Prorifi3D-Official/Prorifi3D-Upgrades/tmp/pdfs/assets-contact-sheet.jpg

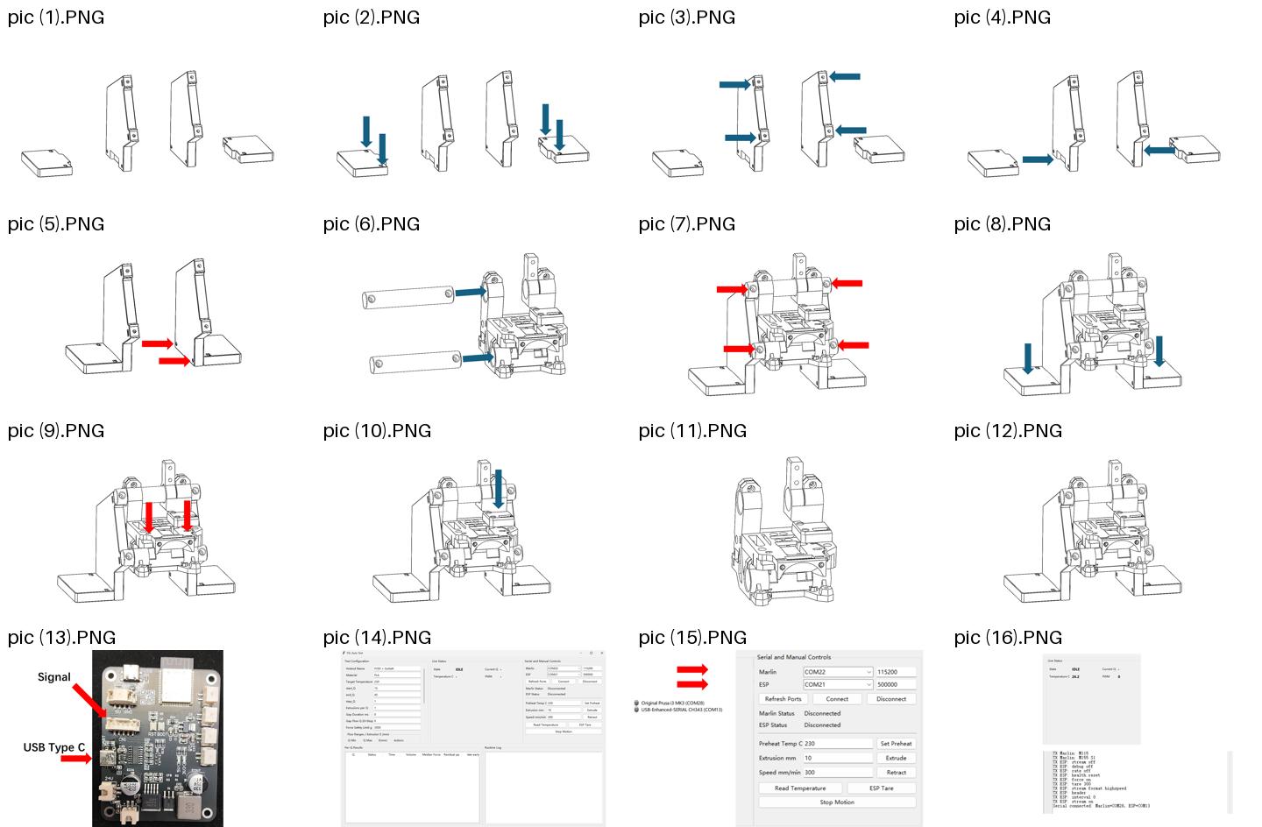
tmp/pdfs/assets-contact-sheet.jpg
