Prorifi3D-Official/Prorifi3D-Upgrades/tmp/pdfs/extracted/page-10-image-01.png

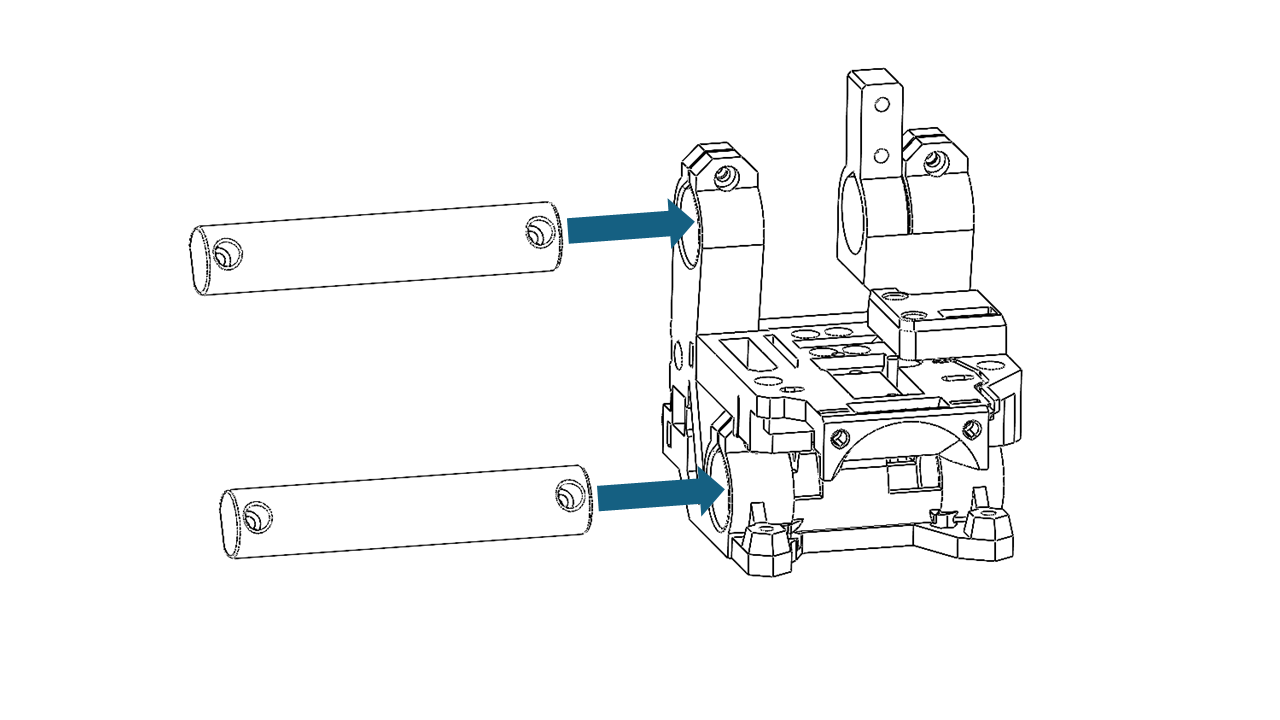
tmp/pdfs/extracted/page-10-image-01.png
