Prorifi3D-Official/Prorifi3D-Upgrades/tmp/pdfs/extracted/page-11-image-02.png

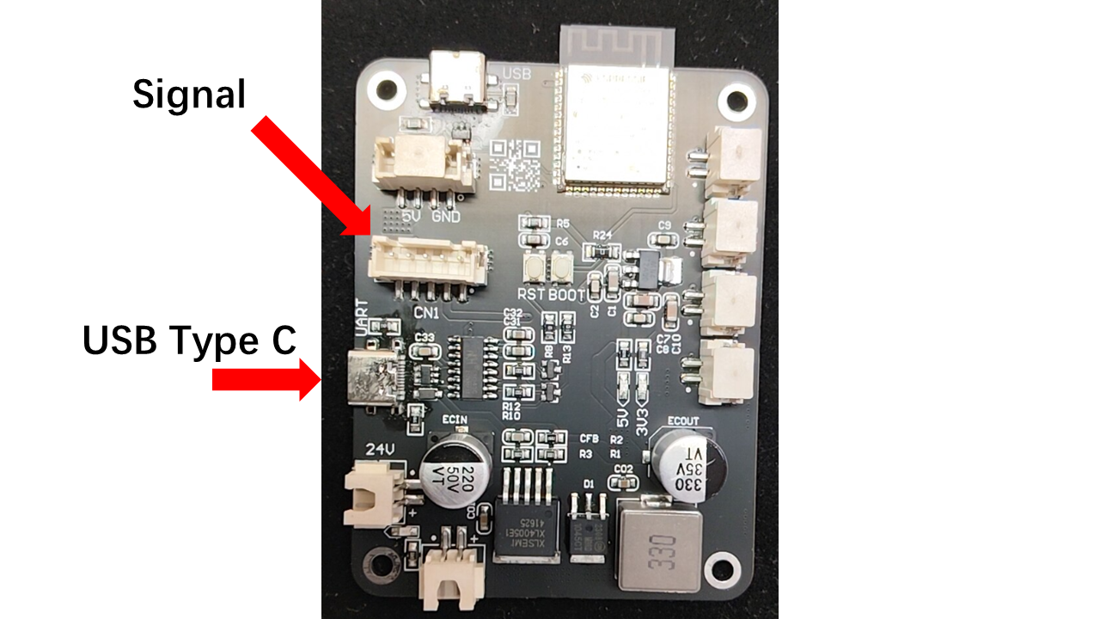
tmp/pdfs/extracted/page-11-image-02.png
