Prorifi3D-Official/Prorifi3D-Upgrades/tmp/pdfs/extracted/page-15-image-02.png

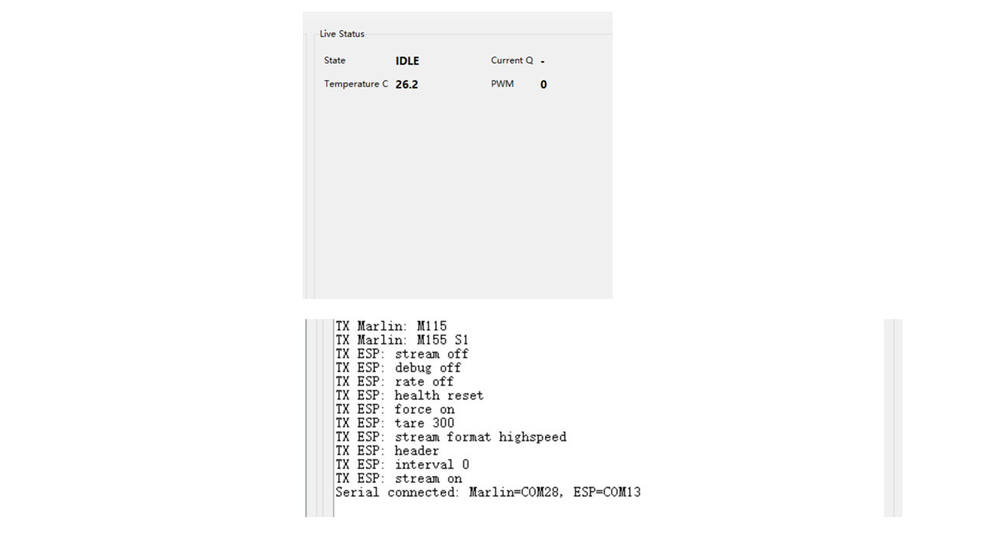
tmp/pdfs/extracted/page-15-image-02.png
