Prorifi3D-Official/Prorifi3D-Upgrades/tmp/pdfs/pdf-pages-contact-sheet.jpg

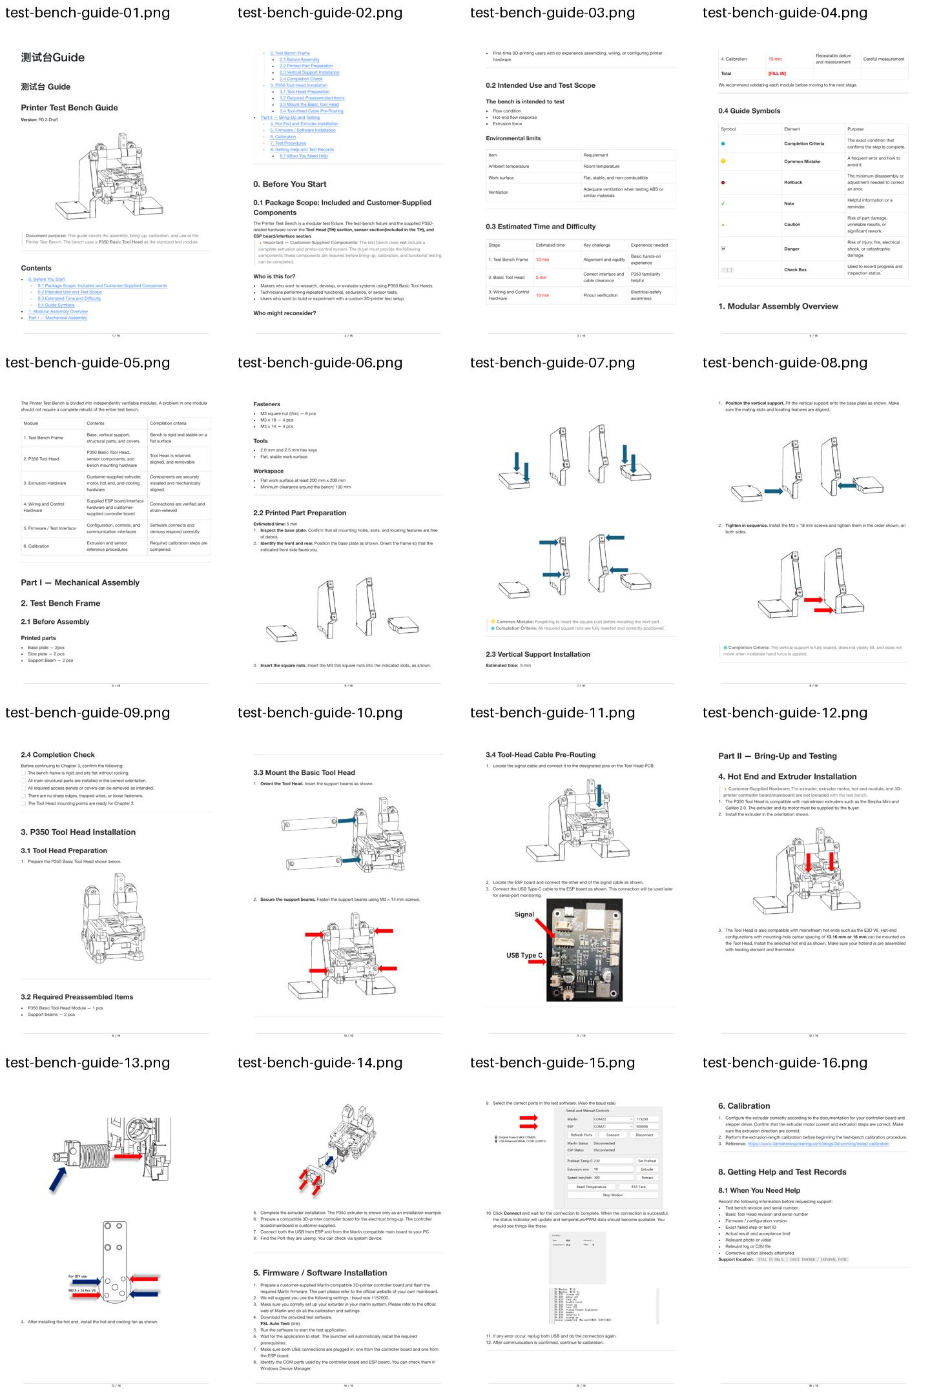
tmp/pdfs/pdf-pages-contact-sheet.jpg
