Prorifi3D-Official/Prorifi3D-Upgrades/tmp/site/src/assets/Dual_Belt_Plus/DB+6.JPG

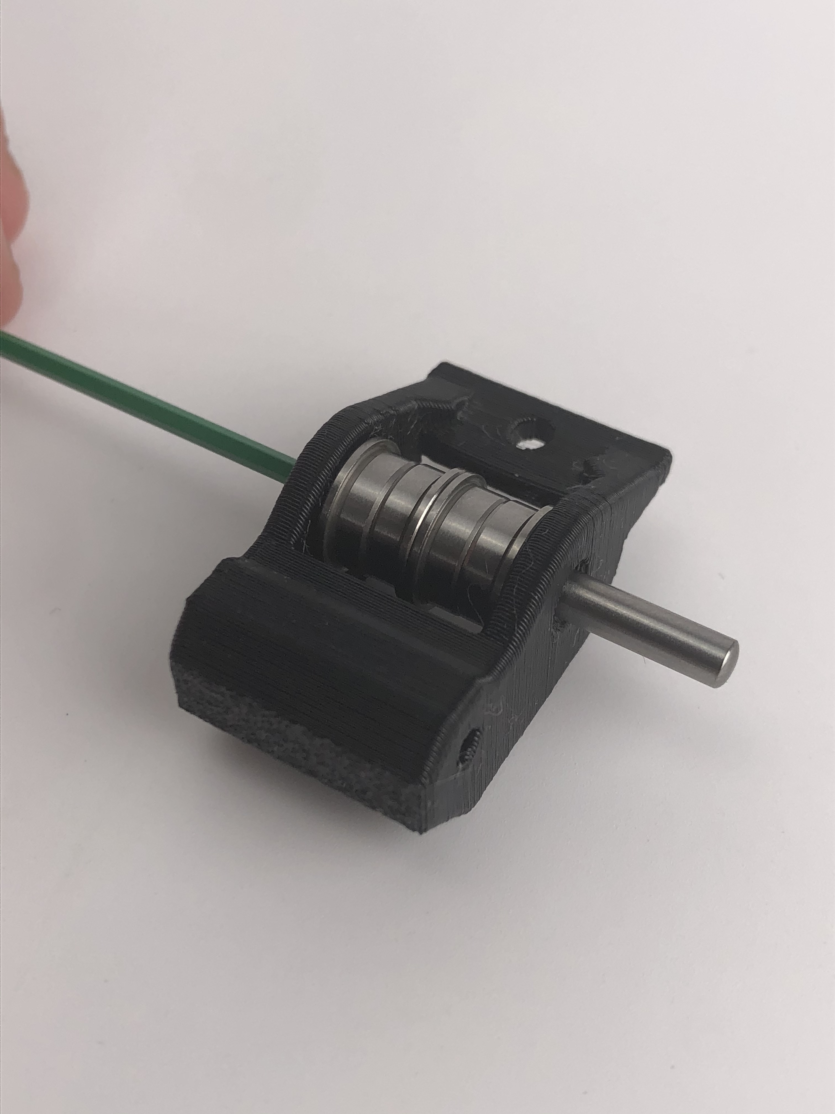
tmp/site/src/assets/Dual_Belt_Plus/DB+6.JPG
