Prorifi3D-Official/Prorifi3D-Upgrades/tmp/site/src/assets/Dual_Belt_Plus/DB+7.JPG

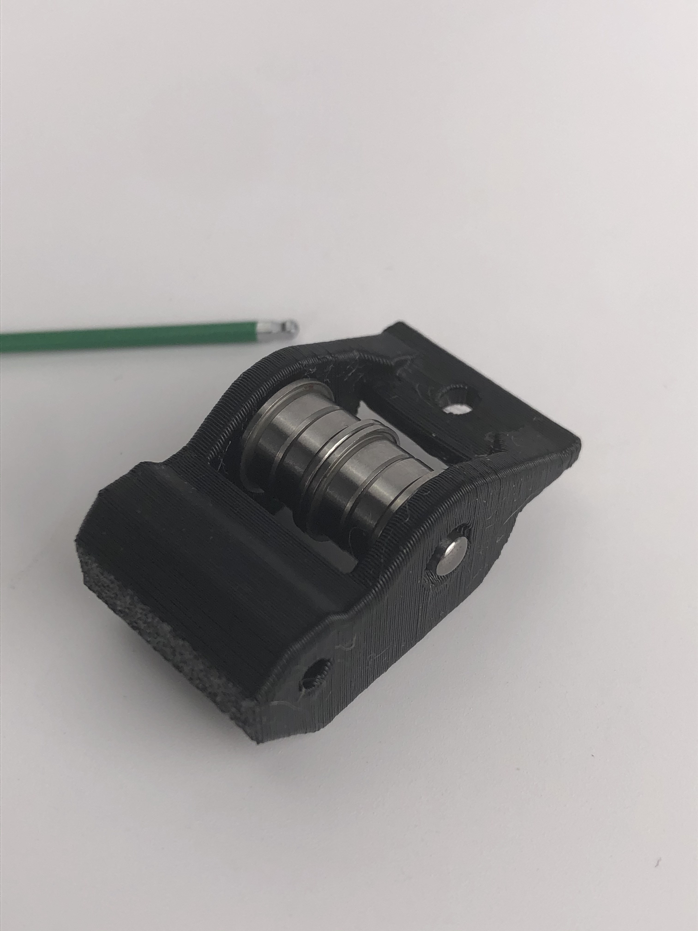
tmp/site/src/assets/Dual_Belt_Plus/DB+7.JPG
