Prorifi3D-Official/Prorifi3D-Upgrades/tmp/site/src/assets/Stage_2/DB_1.png

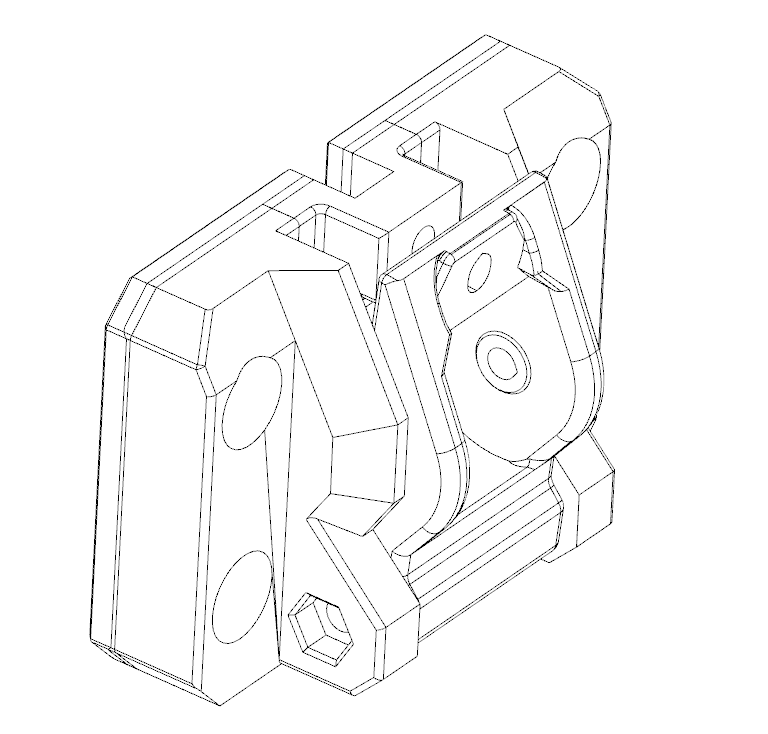
tmp/site/src/assets/Stage_2/DB_1.png
