Prorifi3D-Official/Prorifi3D-Upgrades/tmp/site/src/assets/Stage_2/PSU_2.png

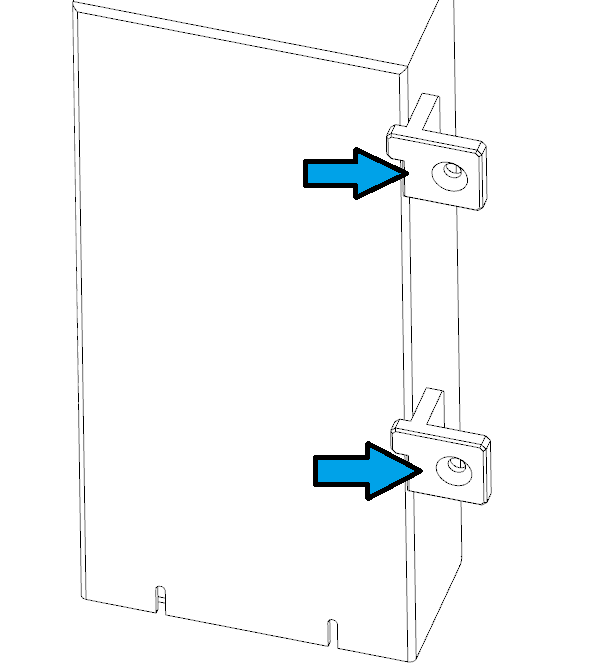
tmp/site/src/assets/Stage_2/PSU_2.png
