Prorifi3D-Official/Prorifi3D-Upgrades/Original i3 series Upgrade Kits/Stage 2 Upgrade/Frame/STL/BLACK/3mf/Spool_holder.3mf

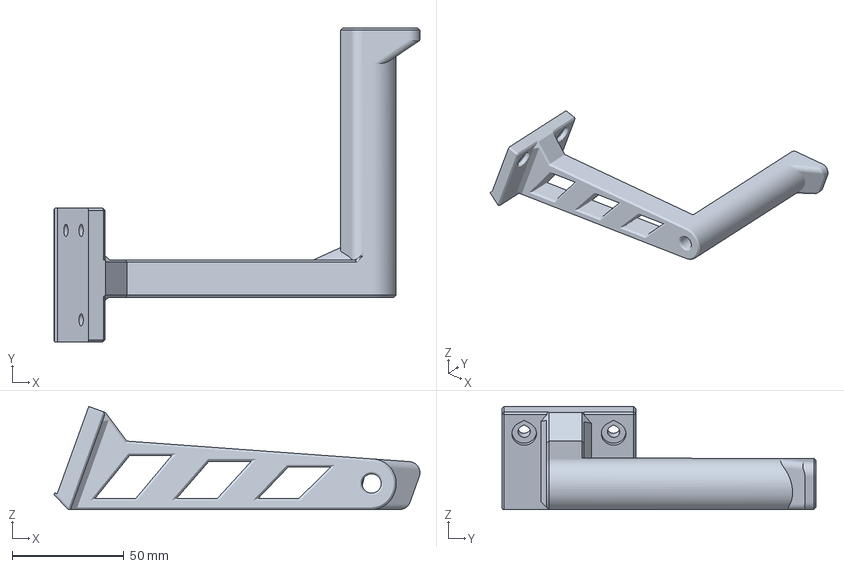
[picture p133: CAD file, 2022-03-23]
Original i3 series Upgrade Kits/Stage 2 Upgrade/Frame/STL/BLACK/3mf/Spool_holder.3mf
163.7 x 140.6 x 46.1 mm
