Prorifi3D-Official/Prorifi3D-Upgrades/Original i3 series Upgrade Kits/Stage 2 Upgrade/Frame/STL/Jigs/Jigs.3mf

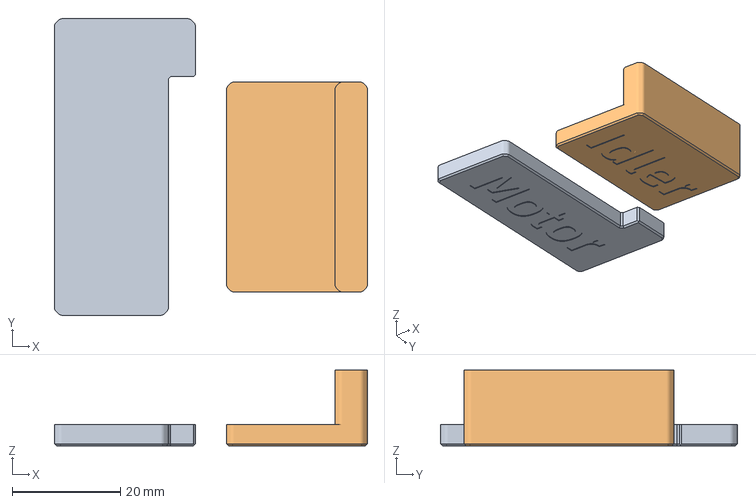
[picture p134: CAD file, 2022-03-23]
Original i3 series Upgrade Kits/Stage 2 Upgrade/Frame/STL/Jigs/Jigs.3mf
57.7 x 54.7 x 14.0 mm
Jig-Motor.stl
Jig-Idler.stl
