Prorifi3D-Official/Prorifi3D-Upgrades/Original i3 series Upgrade Kits/Stage 2 Upgrade/Frame/STL/MIX COLOR/LCD-Cover.stl

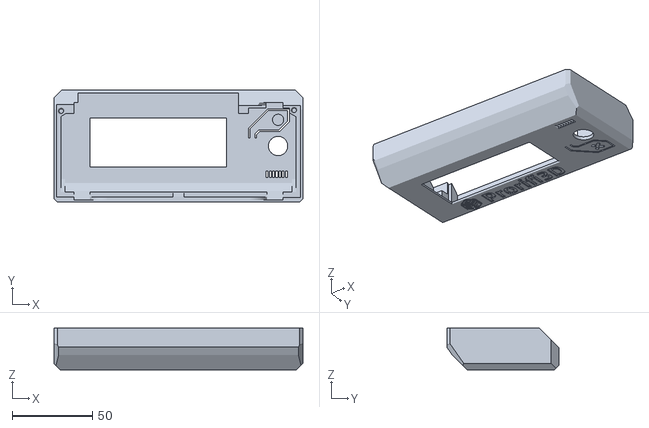
[picture p135: CAD file, 2022-03-23]
Original i3 series Upgrade Kits/Stage 2 Upgrade/Frame/STL/MIX COLOR/LCD-Cover.stl
155.0 x 70.0 x 26.0
