Prorifi3D-Official/Prorifi3D-Upgrades/Original i3 series Upgrade Kits/Stage 2 Upgrade/Frame/STL/WATER BLUE/(4)-Endcover.stl

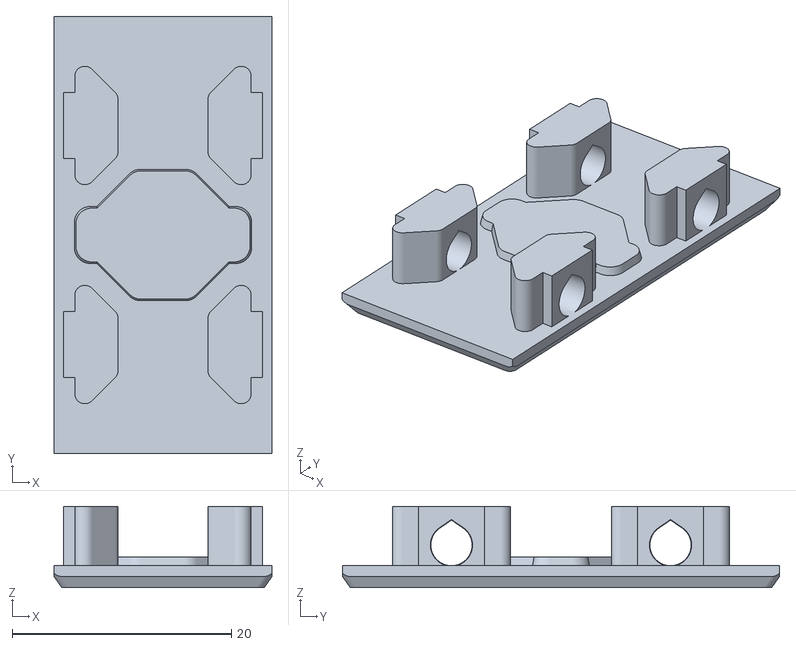
[picture p136: CAD file, 2022-03-23]
Original i3 series Upgrade Kits/Stage 2 Upgrade/Frame/STL/WATER BLUE/(4)-Endcover.stl
19.9 x 39.9 x 7.40
