Prorifi3D-Official/Prorifi3D-Upgrades/Original MINI series Upgrade Kits/MINI Upgrade/Dual Belt/STL/MINI_Y_belt_holder_B.STL

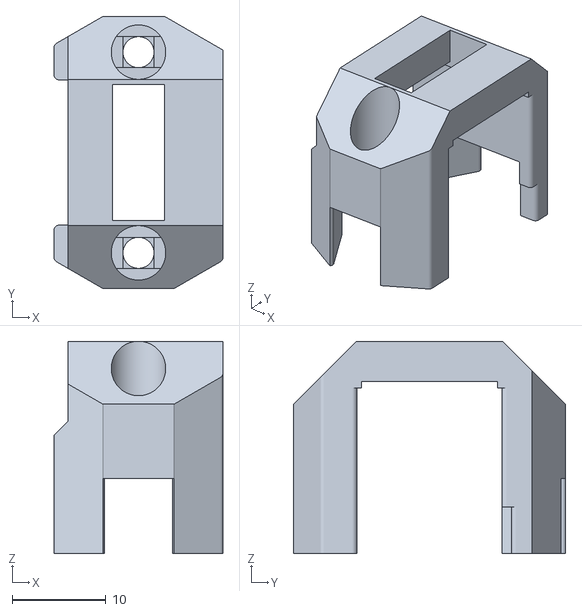
[picture p137: CAD file, 2022-11-03]
Original MINI series Upgrade Kits/MINI Upgrade/Dual Belt/STL/MINI_Y_belt_holder_B.STL
18.0 x 29.0 x 22.7
