Prorifi3D-Official/Prorifi3D-Upgrades/Original i3 series Upgrade Kits/Stage 1 Upgrade/Dual Belt/STEP/Y-Belt-Idler-B.step

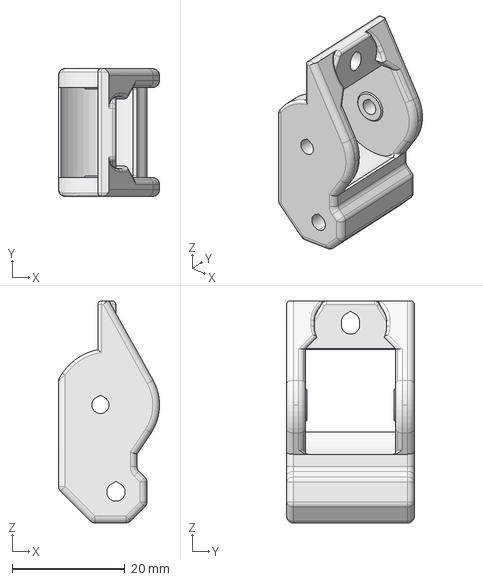
[picture p138: CAD file, 2022-03-23]
Original i3 series Upgrade Kits/Stage 1 Upgrade/Dual Belt/STEP/Y-Belt-Idler-B.step
18.0 x 22.7 x 39.4 mm
