Prorifi3D-Official/Prorifi3D-Upgrades/Original i3 series Upgrade Kits/Stage 2 Upgrade/Frame/STL/BLACK/Electronics-Cover-Holder-B.stl

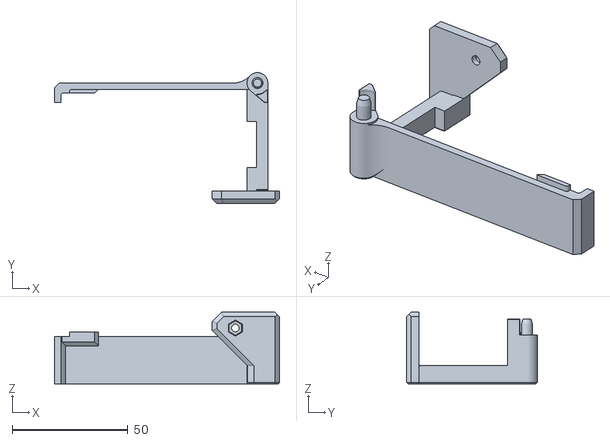
[picture p139: CAD file, 2022-03-23]
Original i3 series Upgrade Kits/Stage 2 Upgrade/Frame/STL/BLACK/Electronics-Cover-Holder-B.stl
97.0 x 56.4 x 31.0
