Prorifi3D-Official/Prorifi3D-Upgrades/Original i3 series Upgrade Kits/Stage 2 Upgrade/Frame/STL/Jigs/Jig-Idler.stl

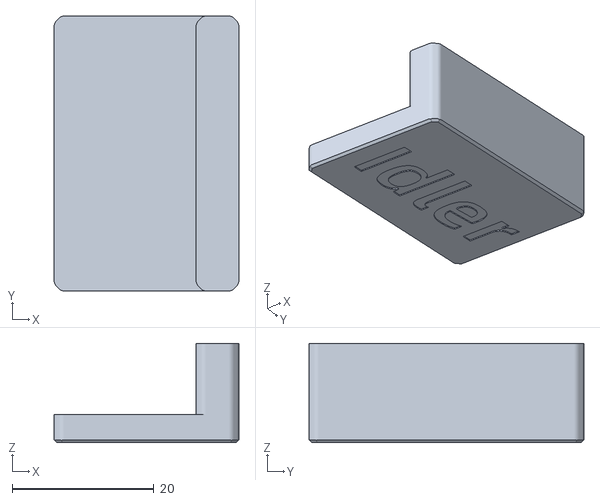
[picture p140: CAD file, 2022-03-23]
Original i3 series Upgrade Kits/Stage 2 Upgrade/Frame/STL/Jigs/Jig-Idler.stl
26.0 x 38.7 x 14.0
