Prorifi3D-Official/Prorifi3D-Upgrades/Original i3 series Upgrade Kits/Stage 2 Upgrade/Frame/STL/WATER BLUE/LCD-Support-A.stl

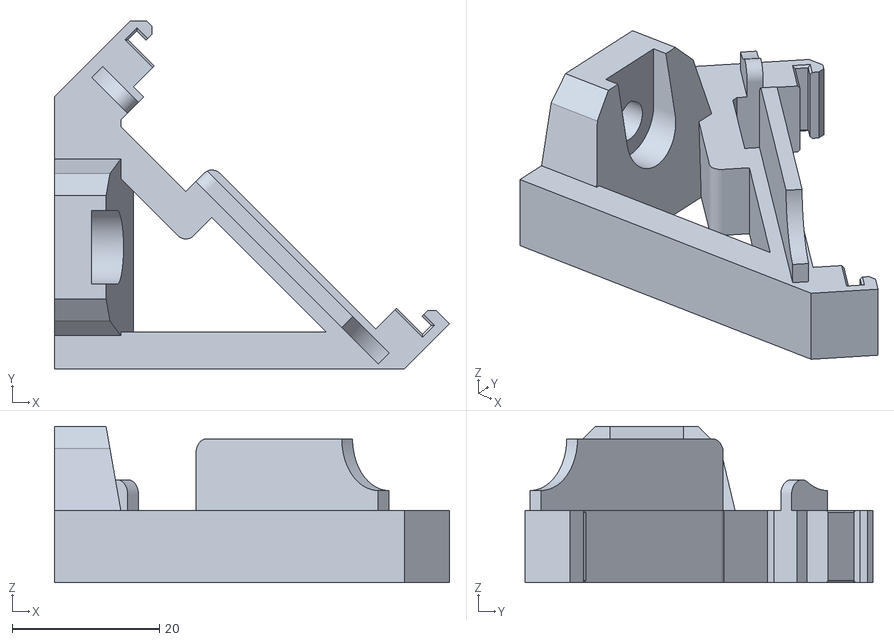
[picture p141: CAD file, 2022-03-23]
Original i3 series Upgrade Kits/Stage 2 Upgrade/Frame/STL/WATER BLUE/LCD-Support-A.stl
53.6 x 47.2 x 21.2
