Prorifi3D-Official/Prorifi3D-Upgrades/Original MINI series Upgrade Kits/MINI Upgrade/Dual Belt/STL/MINI_Y_belt_holder_A.STL

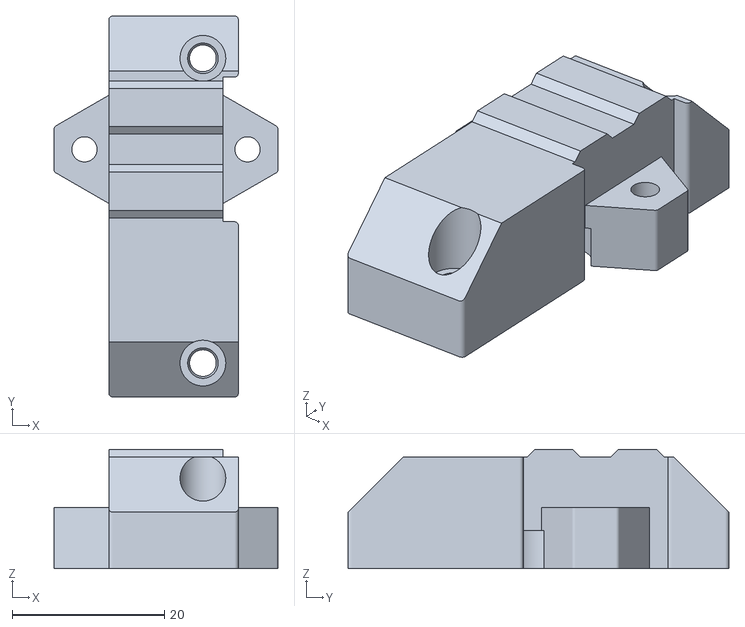
[picture p142: CAD file, 2022-11-03]
Original MINI series Upgrade Kits/MINI Upgrade/Dual Belt/STL/MINI_Y_belt_holder_A.STL
29.4 x 50.0 x 15.6
