Prorifi3D-Official/Prorifi3D-Upgrades/Original i3 series Upgrade Kits/Stage 2 Upgrade/Frame/STL/BLACK/Electronics-Cover-Holder-A.stl

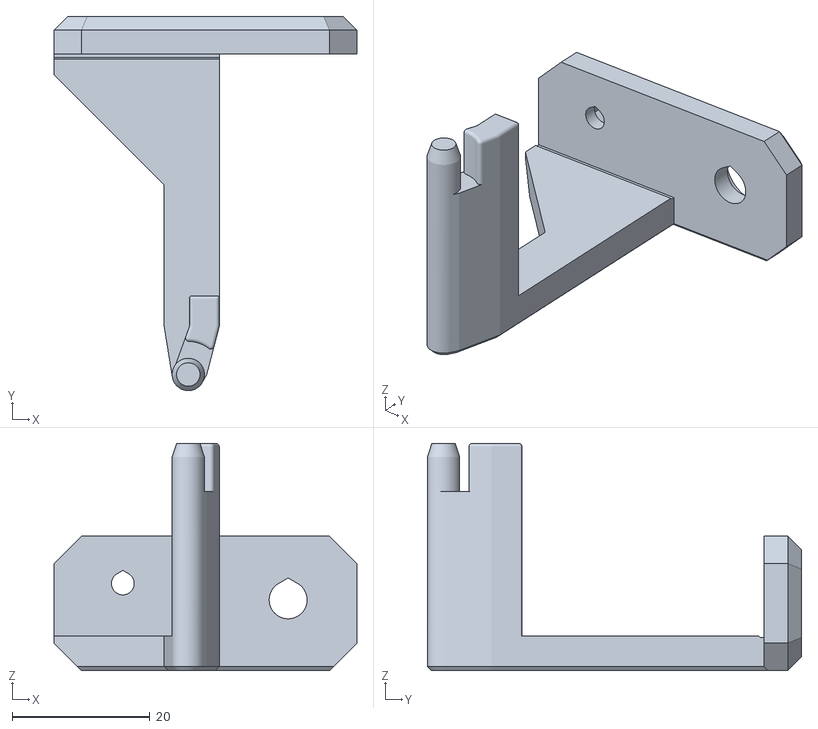
[picture p143: CAD file, 2022-03-23]
Original i3 series Upgrade Kits/Stage 2 Upgrade/Frame/STL/BLACK/Electronics-Cover-Holder-A.stl
44.0 x 54.4 x 33.0
