Prorifi3D-Official/Prorifi3D-Upgrades/Original MINI series Upgrade Kits/MINI Upgrade/Dual Belt/STL/MINI+-Y-idler.STL

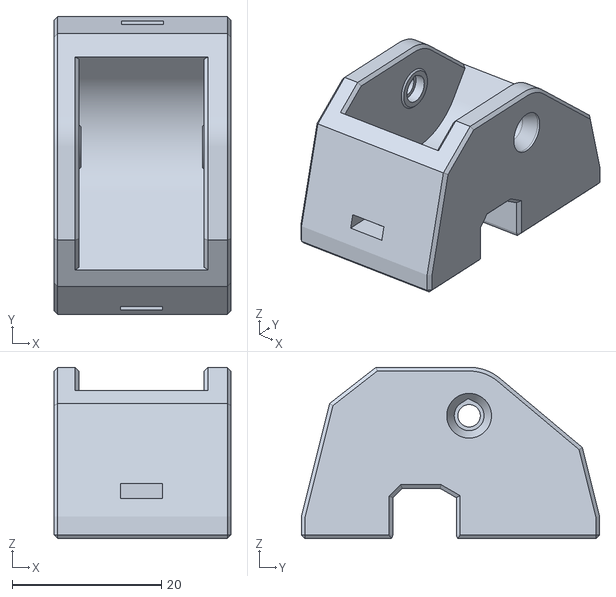
[picture p144: CAD file, 2022-11-01]
Original MINI series Upgrade Kits/MINI Upgrade/Dual Belt/STL/MINI+-Y-idler.STL
23.8 x 40.0 x 23.0
