Prorifi3D-Official/Prorifi3D-Upgrades/Original i3 series Upgrade Kits/Stage 1 Upgrade/Dual Belt/STEP/Y-Belt-Clip.STEP

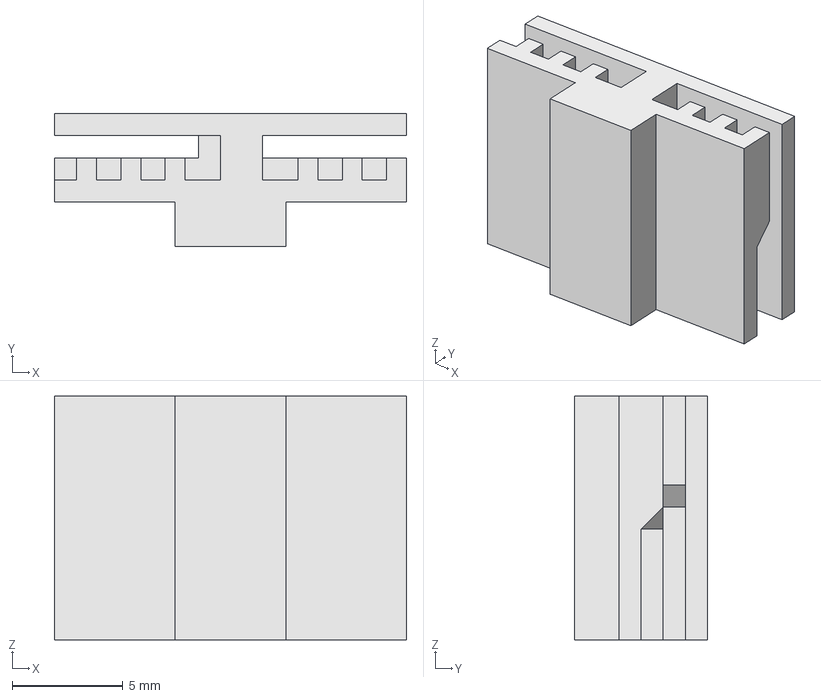
[picture p145: CAD file, 2022-03-23]
Original i3 series Upgrade Kits/Stage 1 Upgrade/Dual Belt/STEP/Y-Belt-Clip.STEP
15.9 x 6.00 x 11.0 mm
