Prorifi3D-Official/Prorifi3D-Upgrades/Original i3 series Upgrade Kits/Stage 2 Upgrade/Frame/STL/BLACK/(2)-Bottomcover.stl

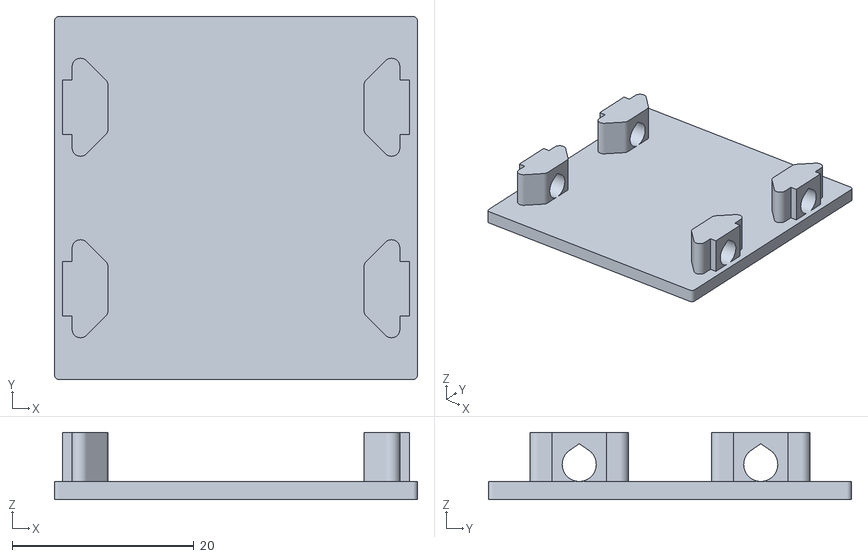
[picture p146: CAD file, 2022-03-23]
Original i3 series Upgrade Kits/Stage 2 Upgrade/Frame/STL/BLACK/(2)-Bottomcover.stl
40.0 x 40.0 x 7.40
