Prorifi3D-Official/Prorifi3D-Upgrades/Original i3 series Upgrade Kits/Stage 2 Upgrade/Frame/STL/WATER BLUE/Y-Belt-Idler-A.stl

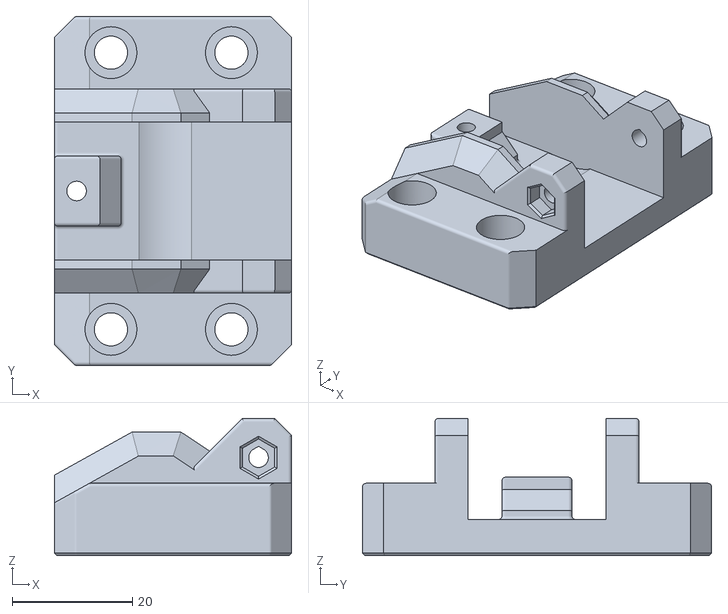
[picture p147: CAD file, 2022-03-23]
Original i3 series Upgrade Kits/Stage 2 Upgrade/Frame/STL/WATER BLUE/Y-Belt-Idler-A.stl
39.4 x 57.9 x 22.8
