Prorifi3D-Official/Prorifi3D-Upgrades/Original i3 series Upgrade Kits/Stage 2 Upgrade/Frame/STL/BLACK/(2)-PSU-Holder.stl

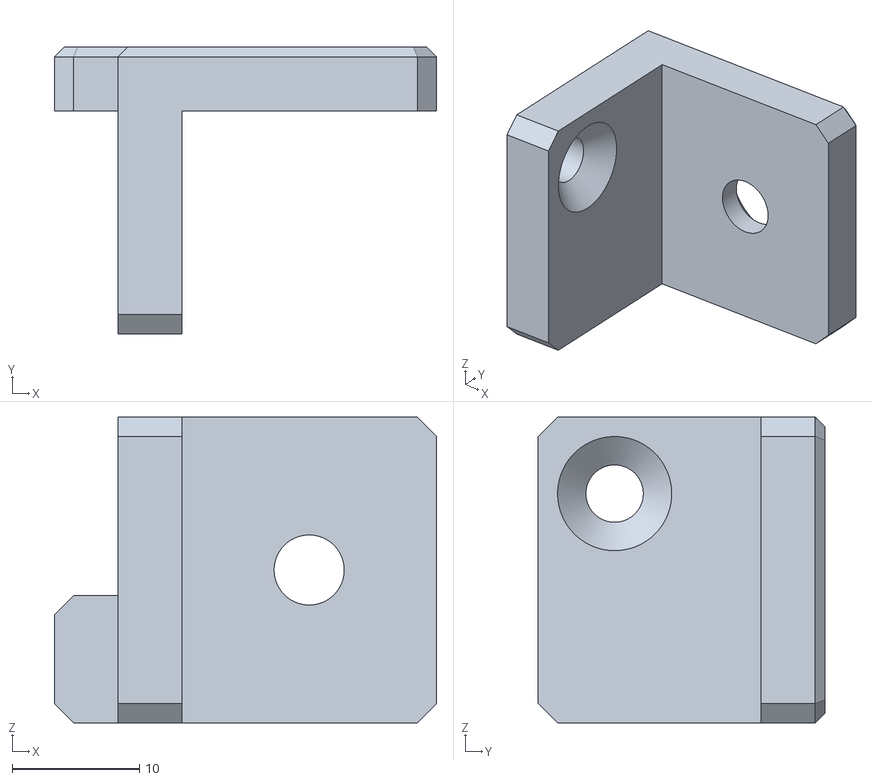
[picture p148: CAD file, 2022-03-23]
Original i3 series Upgrade Kits/Stage 2 Upgrade/Frame/STL/BLACK/(2)-PSU-Holder.stl
30.0 x 22.5 x 24.0
