Prorifi3D-Official/Prorifi3D-Upgrades/tmp/pdfs/test-bench-guide-06.png

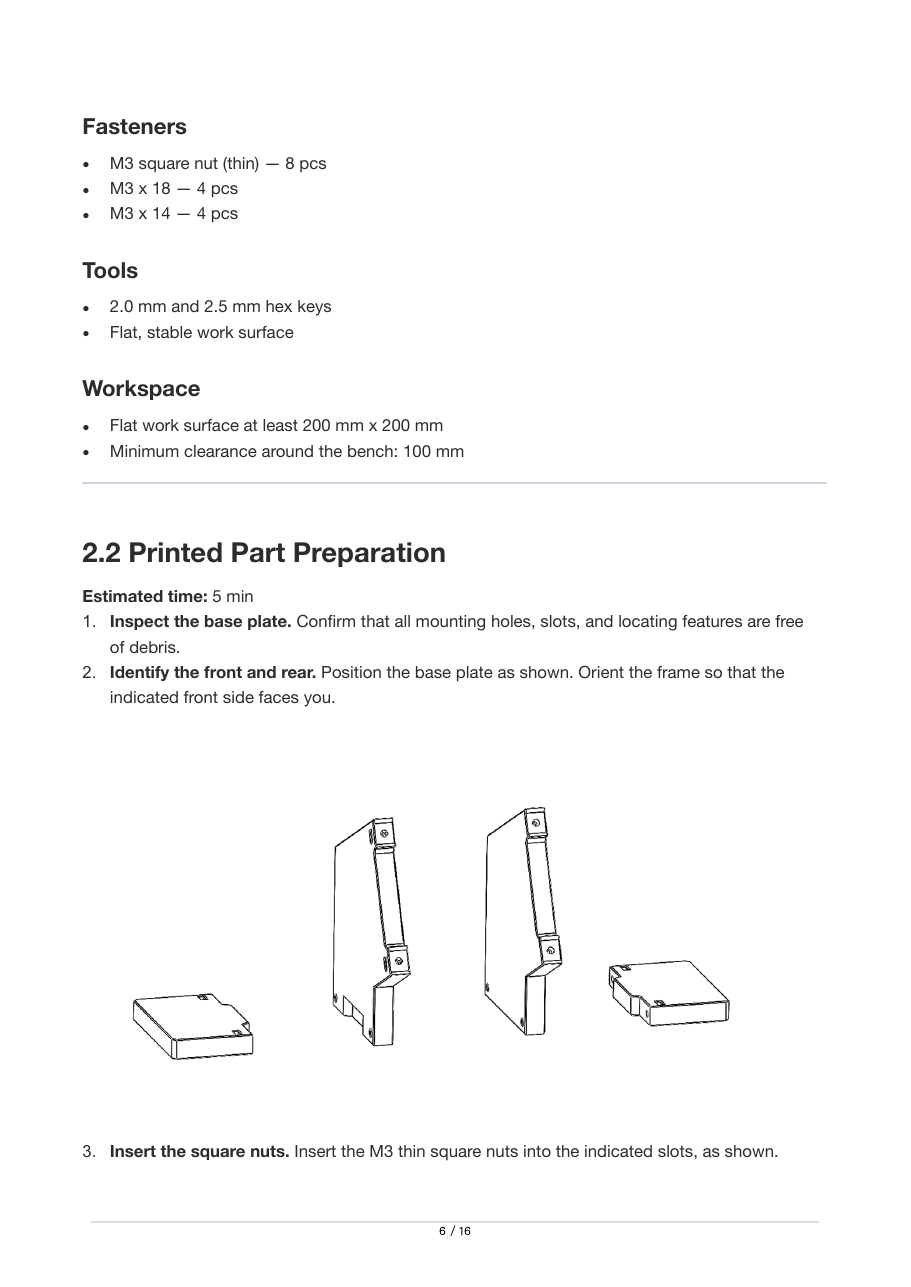
tmp/pdfs/test-bench-guide-06.png
