Prorifi3D-Official/Prorifi3D-Upgrades/tmp/pdfs/test-bench-guide-07.png

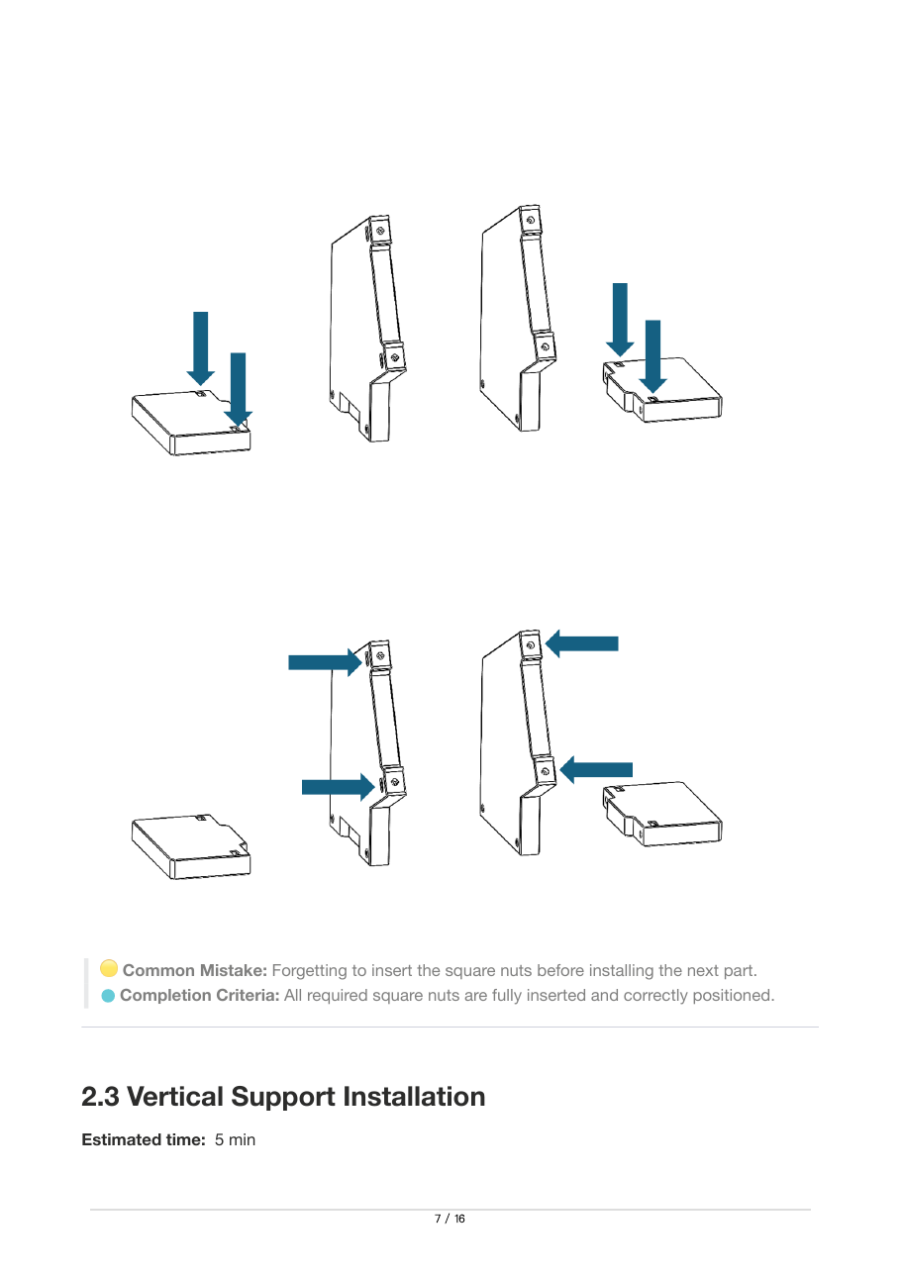
tmp/pdfs/test-bench-guide-07.png
